AcumenDev/FilamentMaker/images/A4988.jpg

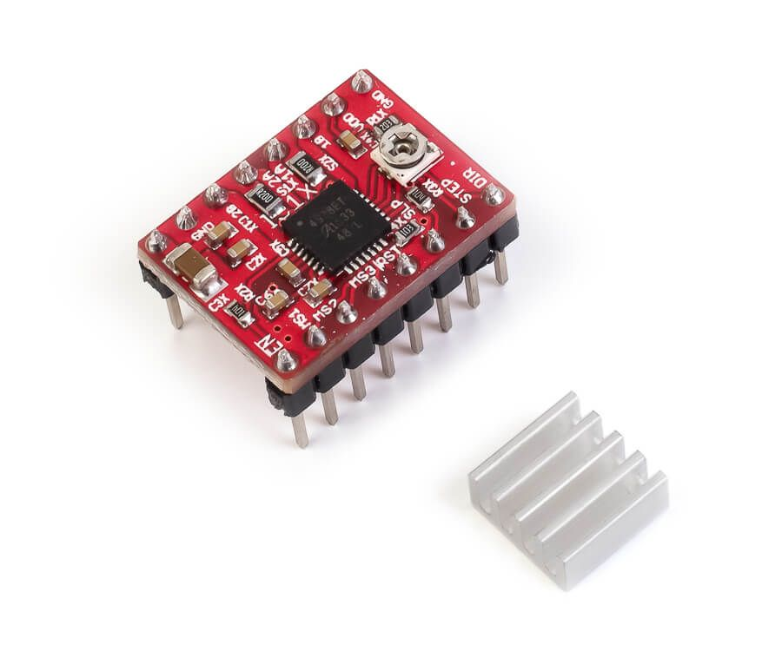
images/A4988.jpg
