AcumenDev/FilamentMaker/images/display.jpg

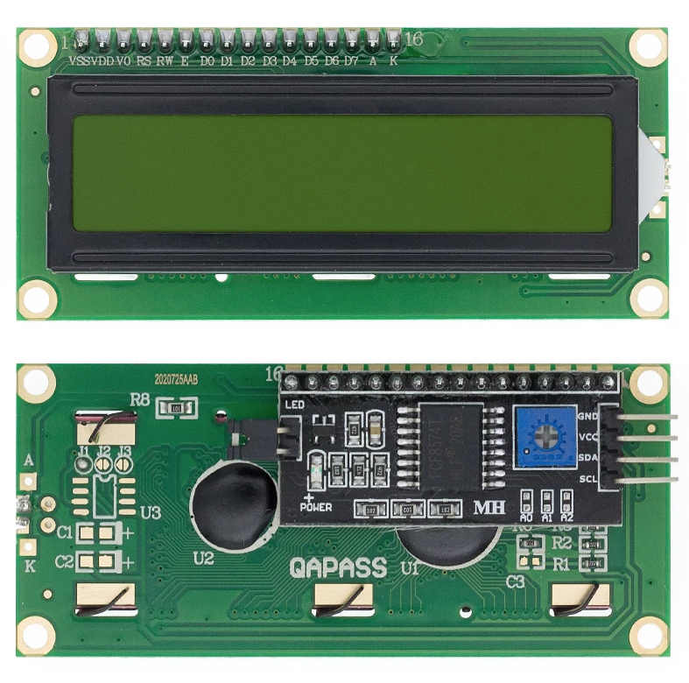
images/display.jpg
