AcumenDev/FilamentMaker/images/DRV8825.jpg

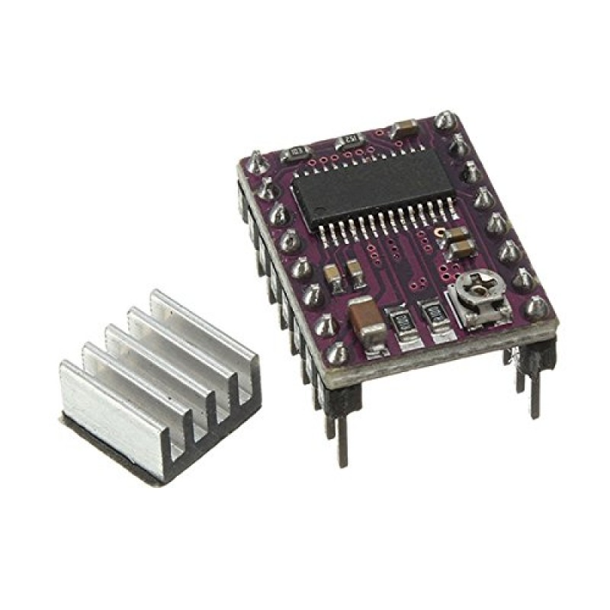
images/DRV8825.jpg
