AcumenDev/FilamentMaker/images/heater.jpg

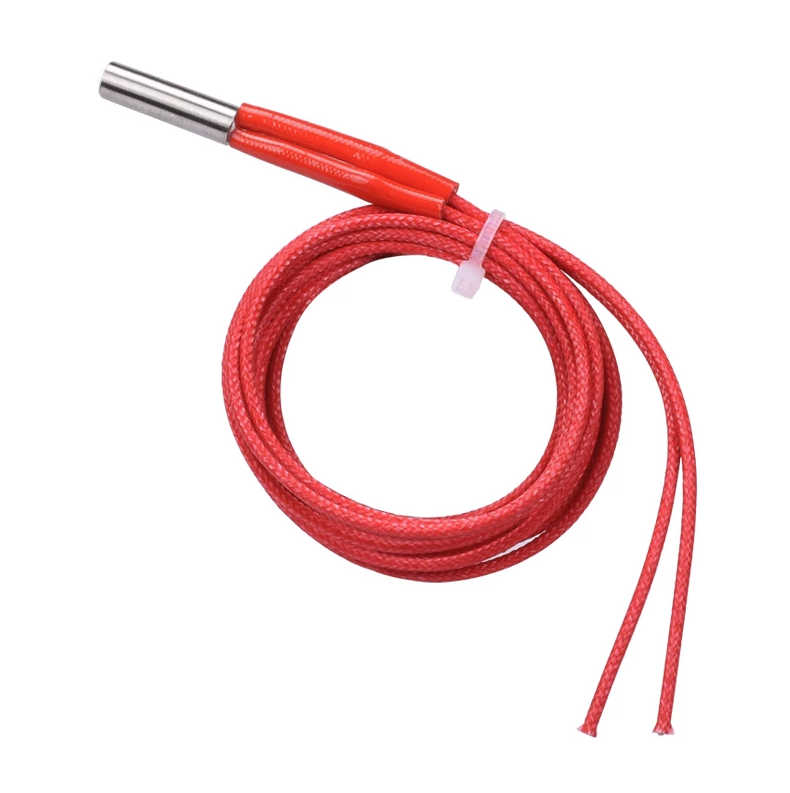
images/heater.jpg
