AcumenDev/FilamentMaker/images/mosfet-board.jpg

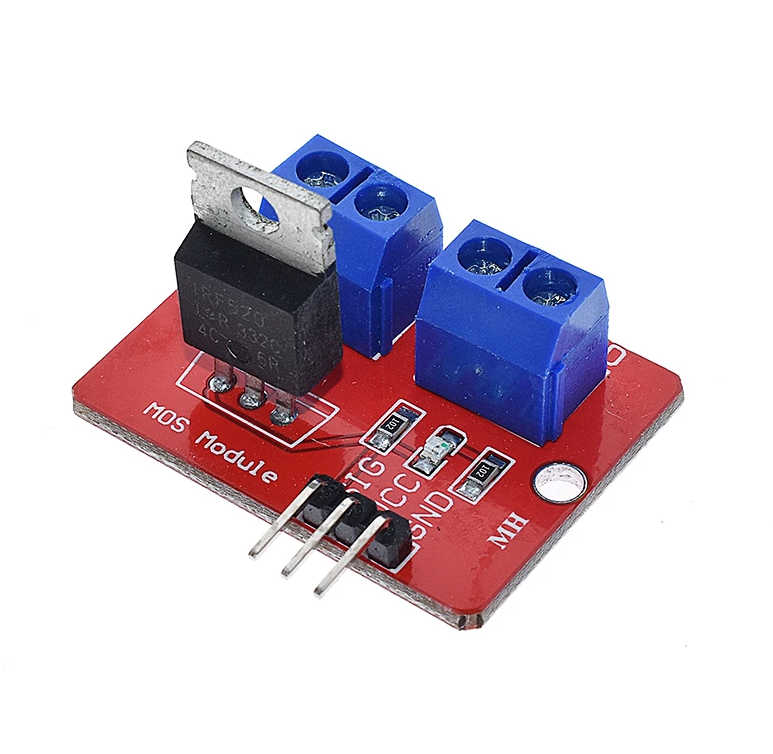
images/mosfet-board.jpg
