AcumenDev/FilamentMaker/images/ntc-termistor-100kom.jpg

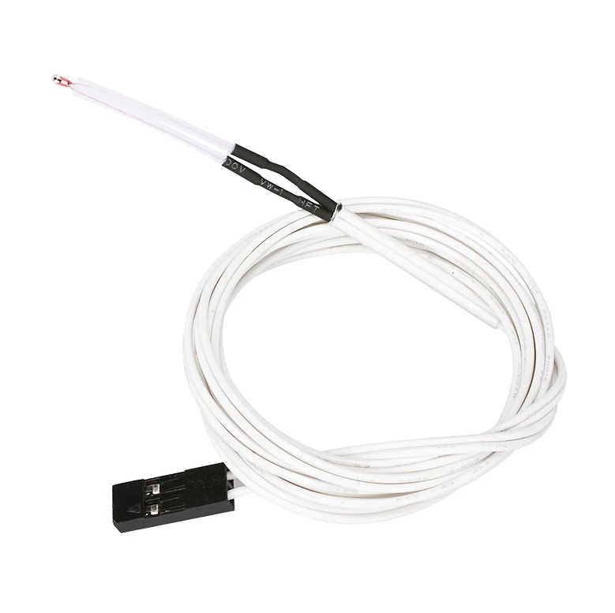
images/ntc-termistor-100kom.jpg
