AcumenDev/FilamentMaker/images/tmc2208.jpg

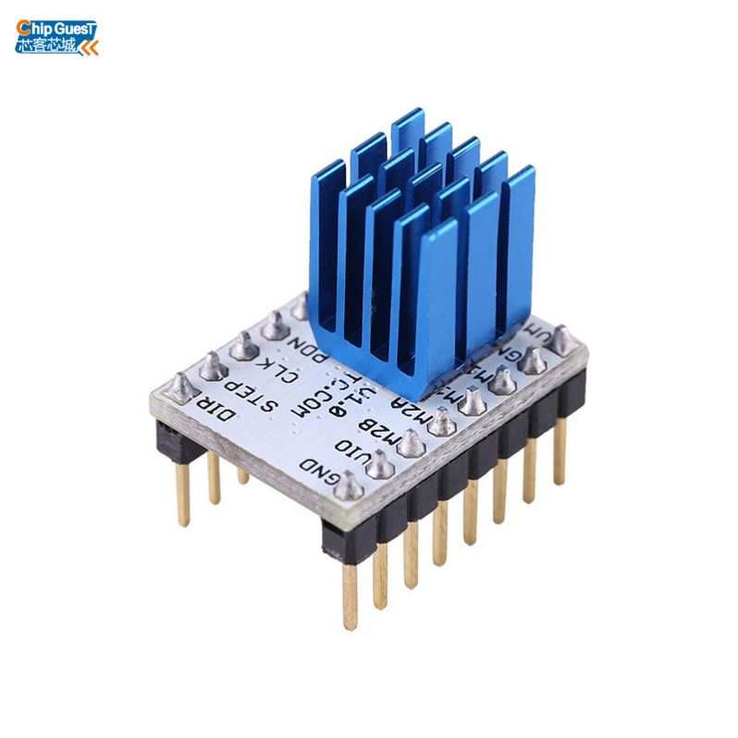
images/tmc2208.jpg
