AcumenDev/FilamentMaker/models/botle_cut/insert_10mm.stl

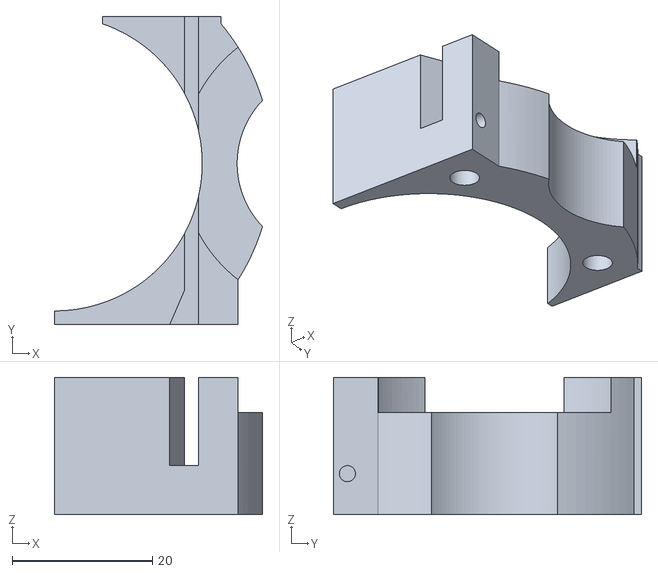
[picture p28: CAD file, 2021-02-14]
models/botle_cut/insert_10mm.stl
29.7 x 44.0 x 19.6
