AcumenDev/FilamentMaker/models/gearbox/new_gear_box_stl/New_gear_box-ModelCoverScreed003.stl

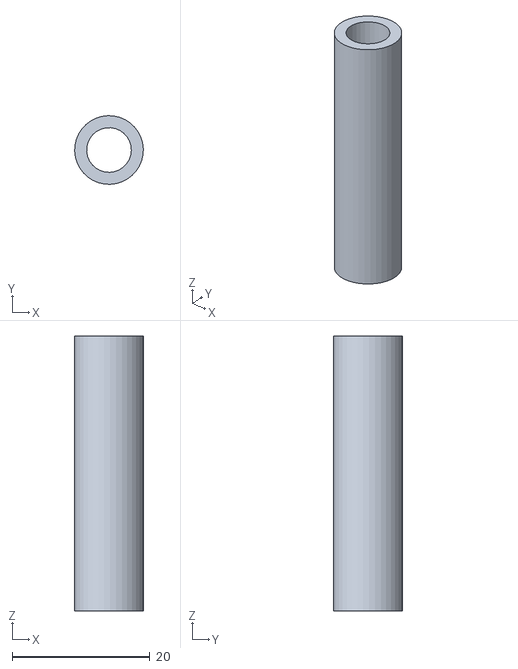
[picture p29: CAD file, 2022-06-27]
models/gearbox/new_gear_box_stl/New_gear_box-ModelCoverScreed003.stl
9.99 x 9.99 x 40.0
