AcumenDev/FilamentMaker/models/gearbox/new_gear_box_stl/New_gear_box-Modelinsert_for_gear_002.stl

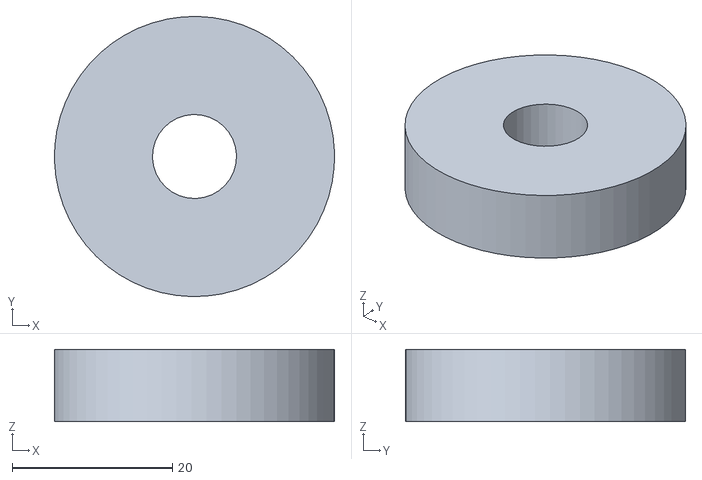
[picture p30: CAD file, 2022-06-27]
models/gearbox/new_gear_box_stl/New_gear_box-Modelinsert_for_gear_002.stl
35.0 x 35.0 x 9.00
