AcumenDev/FilamentMaker/models/gearbox/new_gear_box_stl/New_gear_box-ModelInsert_3_gears_1_001.stl

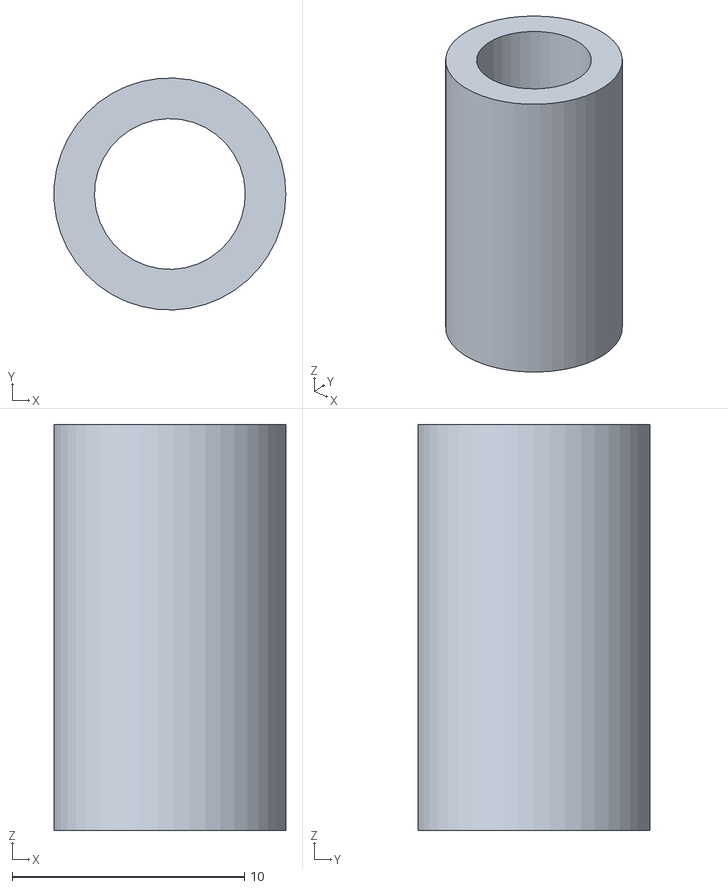
[picture p31: CAD file, 2022-06-27]
models/gearbox/new_gear_box_stl/New_gear_box-ModelInsert_3_gears_1_001.stl
9.99 x 9.99 x 17.5
