AcumenDev/FilamentMaker/models/gearbox/new_gear_box_stl/New_gear_box-ModelSpool__004.stl

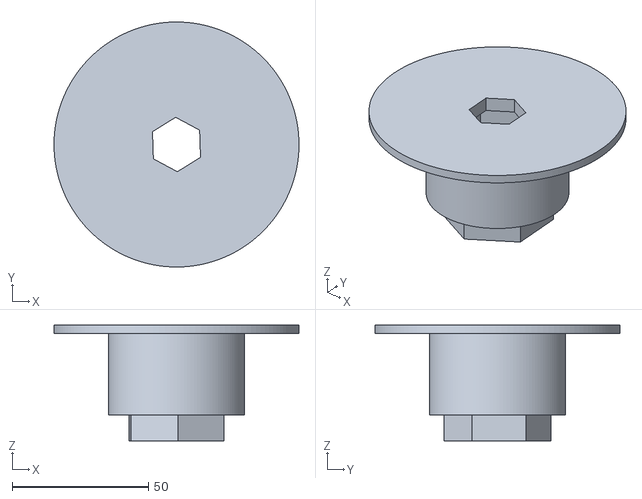
[picture p32: CAD file, 2022-06-27]
models/gearbox/new_gear_box_stl/New_gear_box-ModelSpool__004.stl
90.0 x 90.0 x 42.5
