AcumenDev/FilamentMaker/models/gearbox/new_gear_box_stl/New_gear_box-ModelShell_003.stl

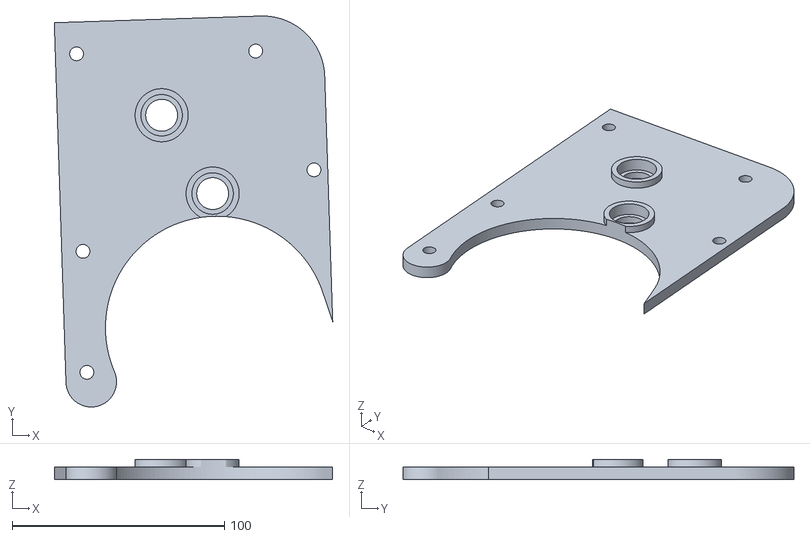
[picture p33: CAD file, 2022-06-27]
models/gearbox/new_gear_box_stl/New_gear_box-ModelShell_003.stl
131.0 x 184.1 x 9.50
