AcumenDev/FilamentMaker/models/gearbox/new_gear_box_stl/New_gear_box-ModelGear001.stl

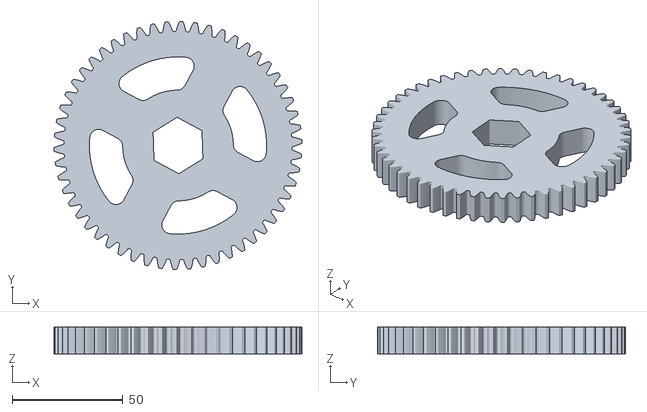
[picture p34: CAD file, 2022-06-27]
models/gearbox/new_gear_box_stl/New_gear_box-ModelGear001.stl
112.0 x 112.0 x 12.0
