AcumenDev/FilamentMaker/models/gearbox/new_gear_box_stl/New_gear_box-ModelSpool__003.stl

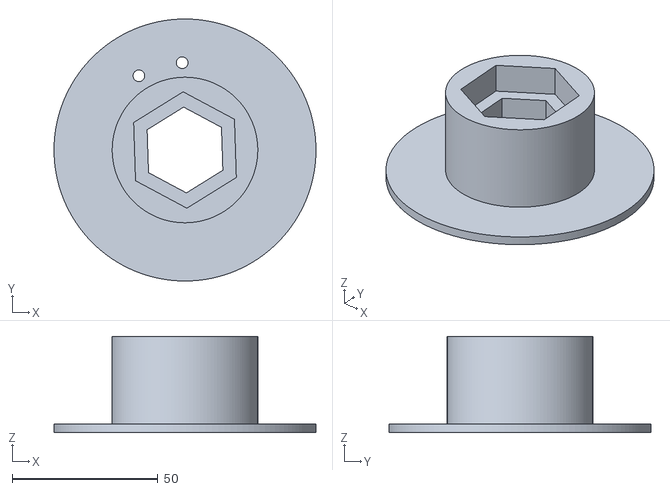
[picture p35: CAD file, 2022-06-27]
models/gearbox/new_gear_box_stl/New_gear_box-ModelSpool__003.stl
90.0 x 90.0 x 33.0
