AcumenDev/FilamentMaker/models/gearbox/new_gear_box_stl/New_gear_box-ModelCap001.stl

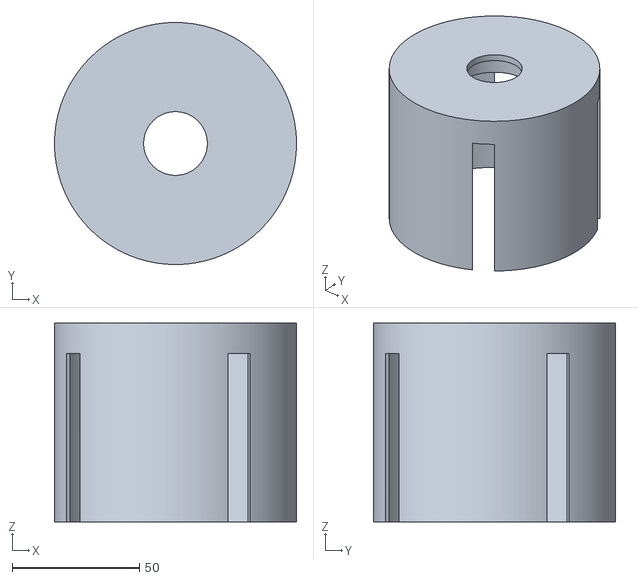
[picture p36: CAD file, 2022-06-27]
models/gearbox/new_gear_box_stl/New_gear_box-ModelCap001.stl
95.0 x 95.0 x 78.0
