AcumenDev/FilamentMaker/models/gearbox/new_gear_box_stl/New_gear_box-ModelInsert_3_gears_2_001.stl

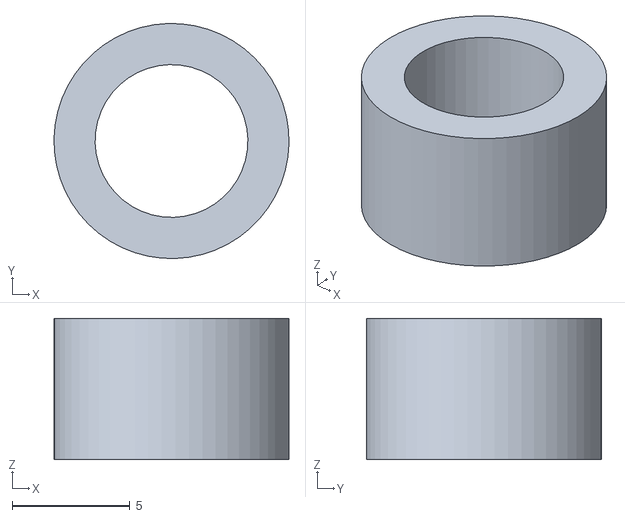
[picture p37: CAD file, 2022-06-27]
models/gearbox/new_gear_box_stl/New_gear_box-ModelInsert_3_gears_2_001.stl
10.00 x 9.99 x 6.00
