AcumenDev/FilamentMaker/models/gearbox/new_gear_box_stl/New_gear_box-ModelInsert_2_gears_1_001.stl

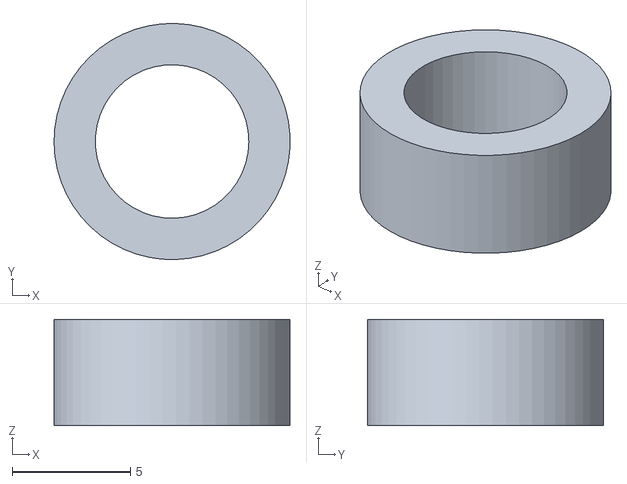
[picture p38: CAD file, 2022-06-27]
models/gearbox/new_gear_box_stl/New_gear_box-ModelInsert_2_gears_1_001.stl
9.99 x 10.00 x 4.50
