AcumenDev/FilamentMaker/models/gearbox/new_gear_box_stl/New_gear_box-ModelShell_1_001.stl

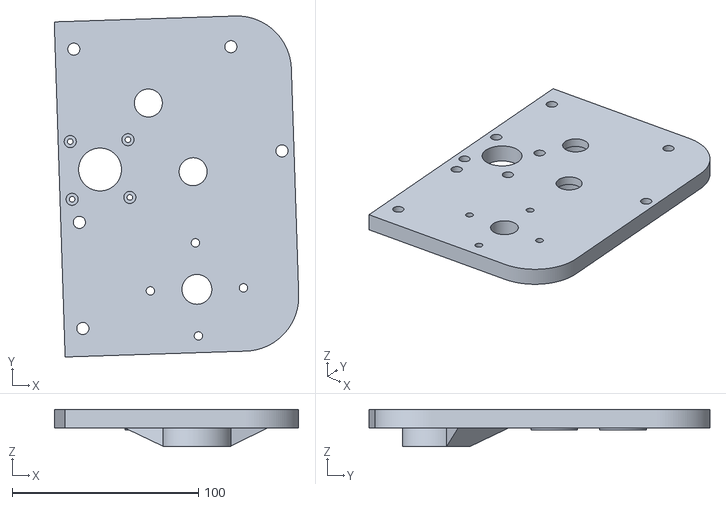
[picture p39: CAD file, 2022-06-27]
models/gearbox/new_gear_box_stl/New_gear_box-ModelShell_1_001.stl
131.3 x 183.1 x 20.0
