AcumenDev/FilamentMaker/models/gearbox/new_gear_box_stl/New_gear_box-ModelClamping_bearing001.stl

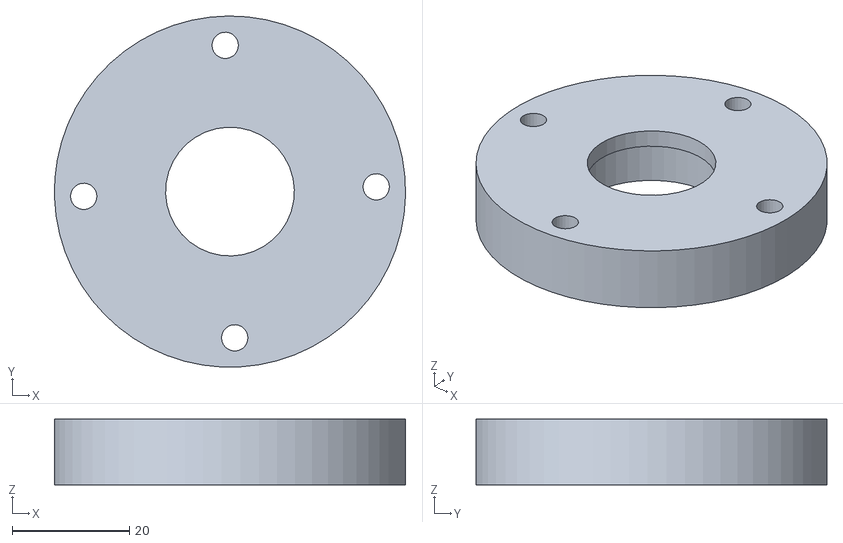
[picture p40: CAD file, 2022-06-27]
models/gearbox/new_gear_box_stl/New_gear_box-ModelClamping_bearing001.stl
60.0 x 60.0 x 11.2
